HisarCS/fablibrary/projects/welcome-space/exports/onshape/v1b_wing_profile.dxf

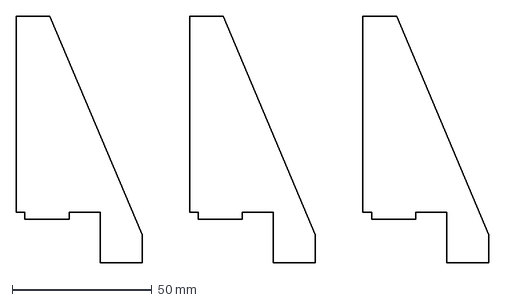
[picture p15: CAD file, 2026-10-07]
projects/welcome-space/exports/onshape/v1b_wing_profile.dxf
169.0 x 88.0 mm
