HisarCS/fablibrary/projects/welcome-space/3d/preview/v1b_wing_preview.stl

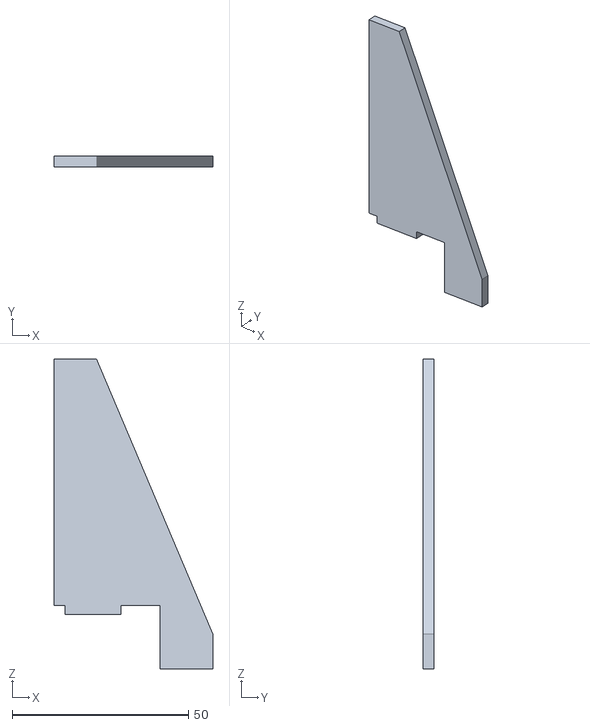
[picture p16: CAD file, 2026-10-01]
projects/welcome-space/3d/preview/v1b_wing_preview.stl
45.0 x 3.00 x 88.0
