HisarCS/fablibrary/projects/welcome-space/exports/dxf/v1b_copper_rails_gs24_cut.dxf

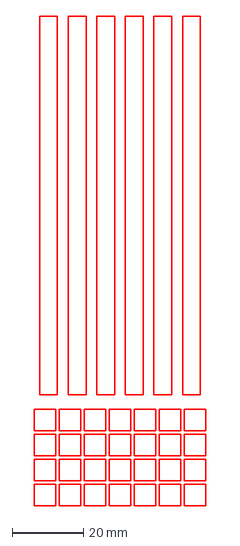
[picture p17: CAD file, 2026-10-07]
projects/welcome-space/exports/dxf/v1b_copper_rails_gs24_cut.dxf
48.0 x 137.0 mm
