HisarCS/fablibrary/projects/welcome-space/exports/onshape/v1_panel_profile.dxf

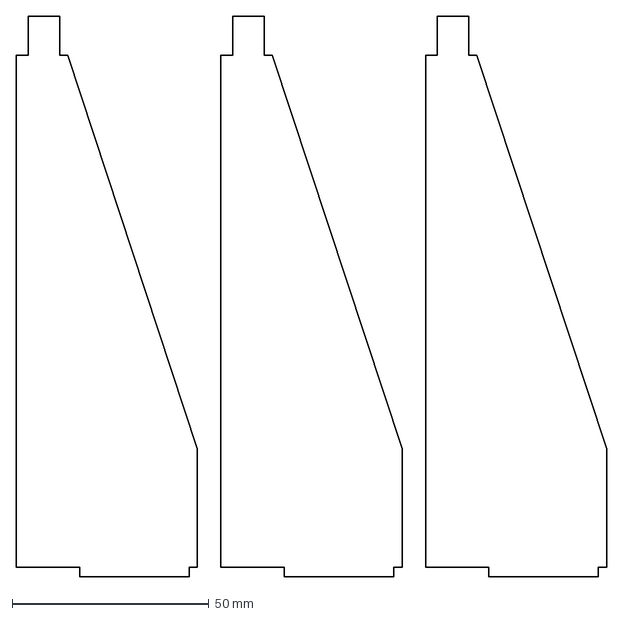
[picture p18: CAD file, 2026-10-07]
projects/welcome-space/exports/onshape/v1_panel_profile.dxf
150.0 x 142.5 mm
