HisarCS/fablibrary/projects/welcome-space/3d/preview/v1b_base_plate_preview.stl

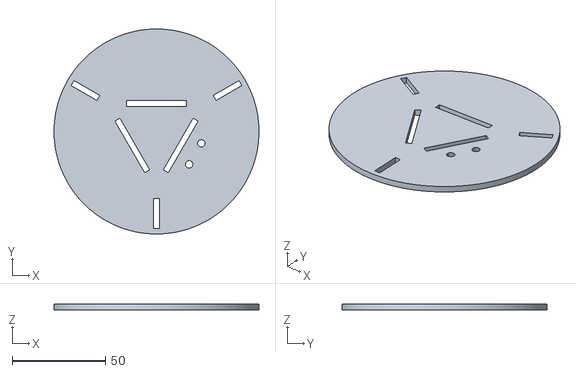
[picture p19: CAD file, 2026-10-01]
projects/welcome-space/3d/preview/v1b_base_plate_preview.stl
110.0 x 110.0 x 3.00
