HisarCS/fablibrary/projects/welcome-space/exports/dxf/v1_base_plate_laser.dxf

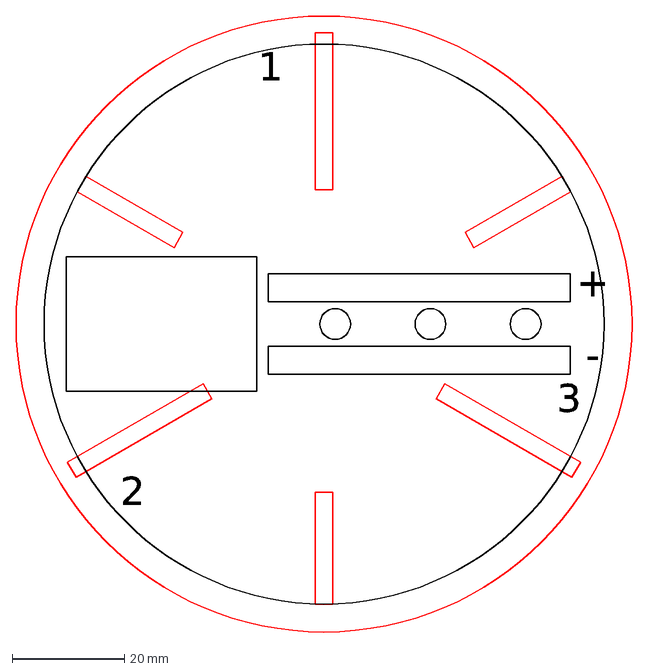
[picture p20: CAD file, 2026-10-07]
projects/welcome-space/exports/dxf/v1_base_plate_laser.dxf
+
-
1
2
3
