HisarCS/fablibrary/projects/welcome-space/exports/onshape/v1_nose_cone_profile.dxf

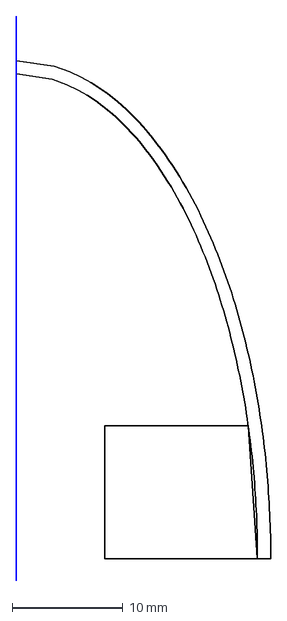
[picture p21: CAD file, 2026-10-07]
projects/welcome-space/exports/onshape/v1_nose_cone_profile.dxf
23.0 x 51.0 mm
