HisarCS/fablibrary/projects/welcome-space/exports/dxf/v1_sticker_sheet_print_cut.dxf

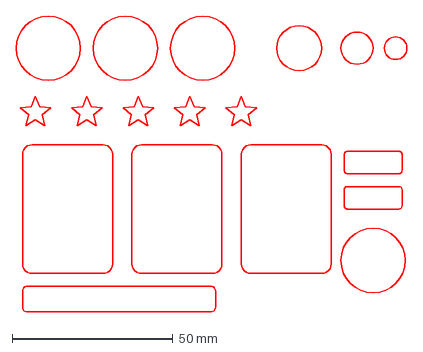
[picture p22: CAD file, 2026-10-07]
projects/welcome-space/exports/dxf/v1_sticker_sheet_print_cut.dxf
121.5 x 92.0 mm
