HisarCS/fablibrary/projects/welcome-space/exports/onshape/v1b_nose_cone_profile.dxf

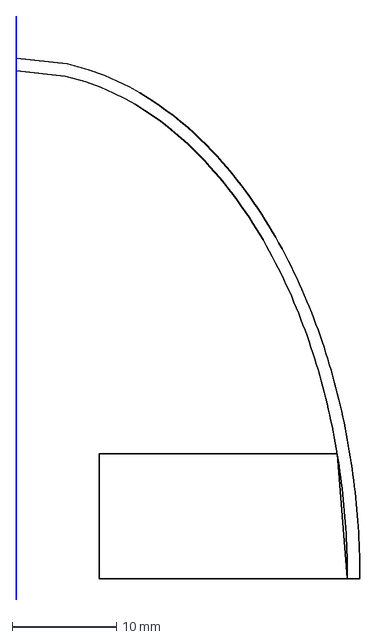
[picture p23: CAD file, 2026-10-07]
projects/welcome-space/exports/onshape/v1b_nose_cone_profile.dxf
33.0 x 56.0 mm
