HisarCS/fablibrary/projects/welcome-space/3d/preview/v1_wing_preview.stl

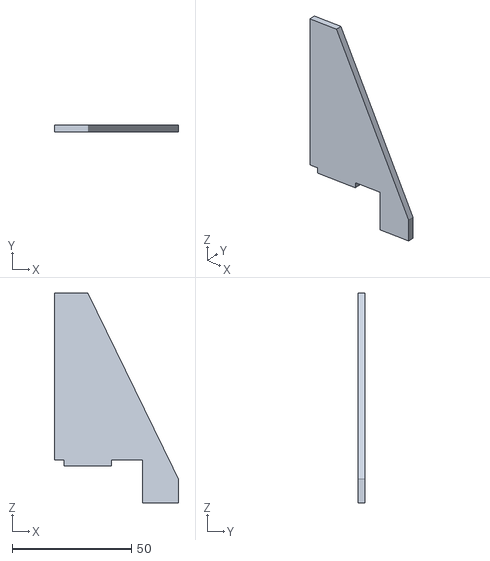
[picture p24: CAD file, 2026-10-01]
projects/welcome-space/3d/preview/v1_wing_preview.stl
52.0 x 3.00 x 88.0
