HisarCS/fablibrary/projects/welcome-space/exports/dxf/v1b_panels_set_laser.dxf

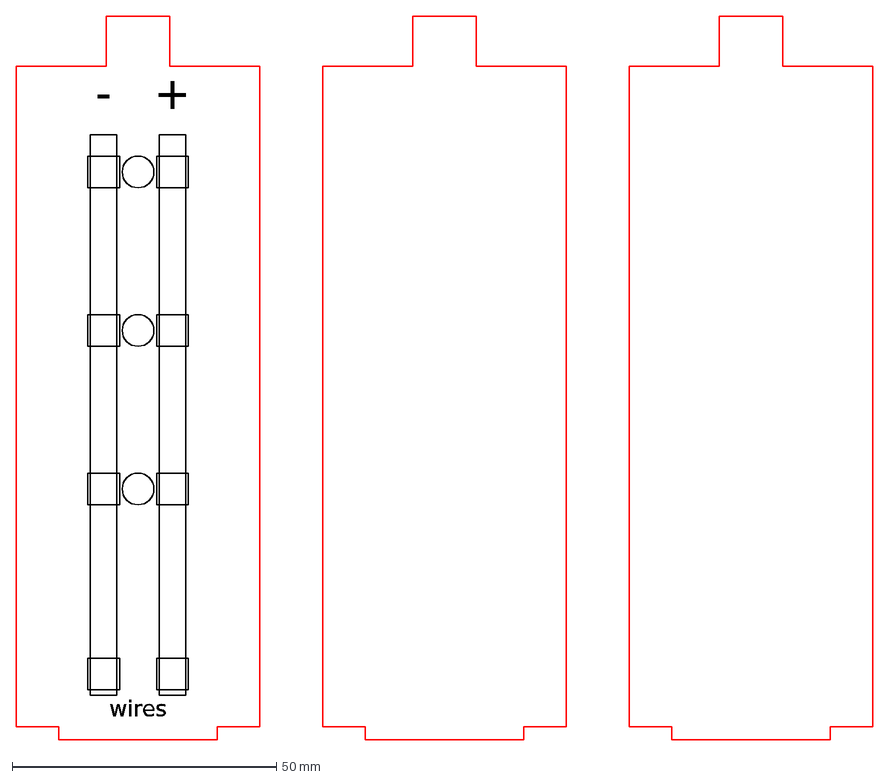
[picture p25: CAD file, 2026-10-07]
projects/welcome-space/exports/dxf/v1b_panels_set_laser.dxf
+
-
wires
