HisarCS/fablibrary/projects/welcome-space/3d/preview/v1_nose_cone_preview.stl

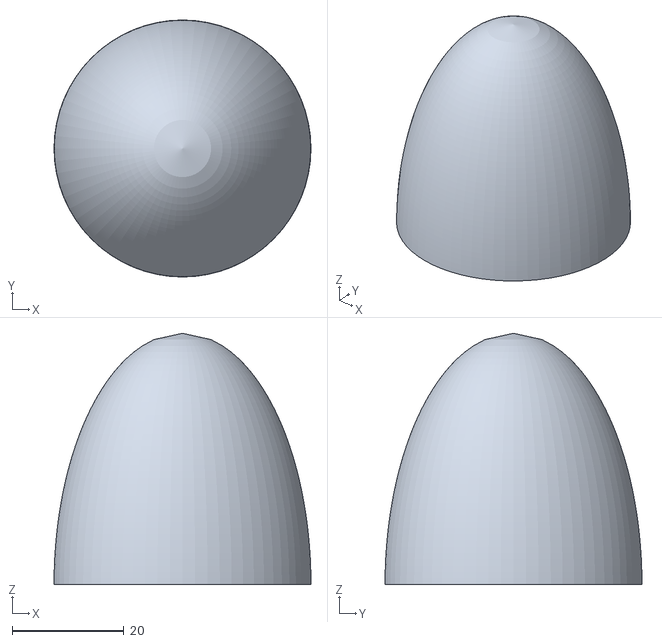
[picture p27: CAD file, 2026-10-01]
projects/welcome-space/3d/preview/v1_nose_cone_preview.stl
46.0 x 46.0 x 45.0
