HisarCS/fablibrary/projects/welcome-space/exports/dxf/v1_wing_laser.dxf

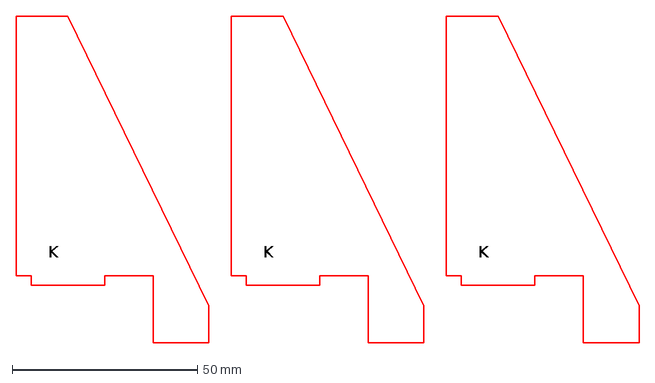
[picture p28: CAD file, 2026-10-07]
projects/welcome-space/exports/dxf/v1_wing_laser.dxf
K
