HisarCS/fablibrary/projects/welcome-space/exports/onshape/v1b_base_plate_profile.dxf

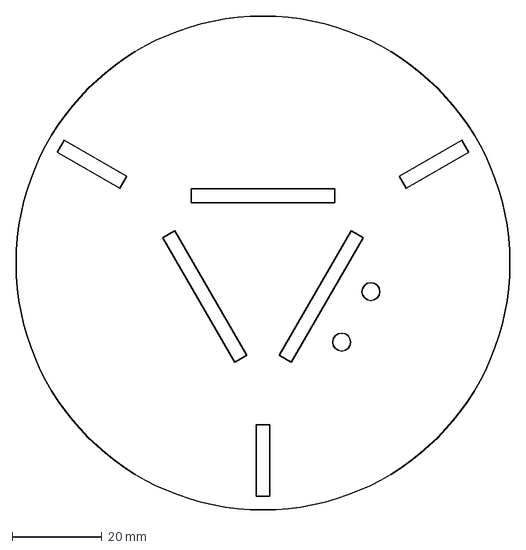
[picture p29: CAD file, 2026-10-07]
projects/welcome-space/exports/onshape/v1b_base_plate_profile.dxf
110.0 x 110.0 mm
