HisarCS/fablibrary/projects/welcome-space/3d/preview/v1_panel_preview.stl

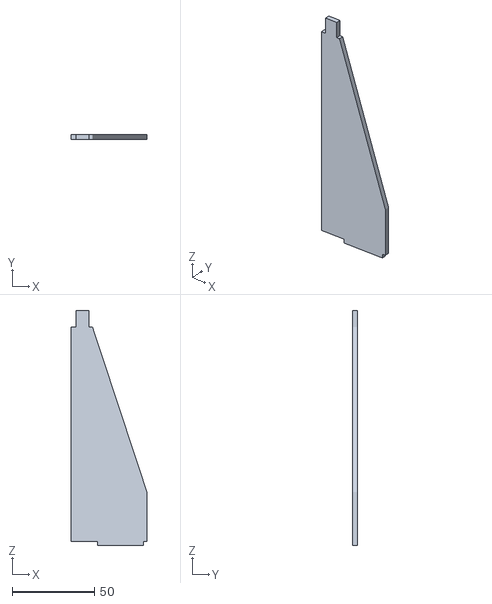
[picture p31: CAD file, 2026-10-01]
projects/welcome-space/3d/preview/v1_panel_preview.stl
46.0 x 3.00 x 142.5
